jbuck2005/brio_compatible_builder_series/stl_files/beams/beam_slotted_20.stl

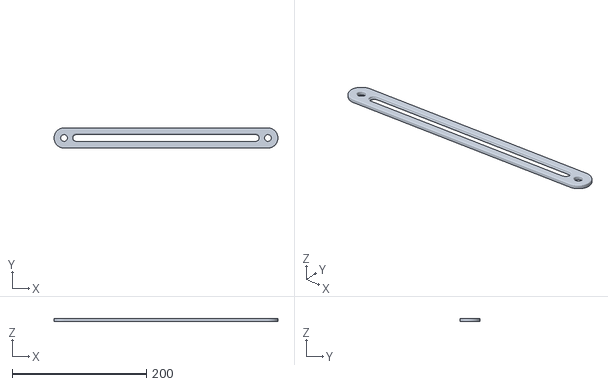
[picture p25: CAD file, 2021-01-02]
stl_files/beams/beam_slotted_20.stl
334.0 x 30.0 x 5.00
