jbuck2005/brio_compatible_builder_series/stl_files/gears/gear_double_idler_20_25.stl

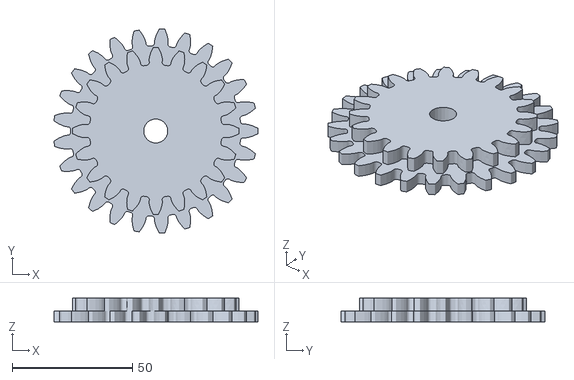
[picture p26: CAD file, 2021-01-02]
stl_files/gears/gear_double_idler_20_25.stl
84.8 x 85.0 x 9.90
