jbuck2005/brio_compatible_builder_series/stl_files/wheels_and_pulleys/pulley_v_60mm.stl

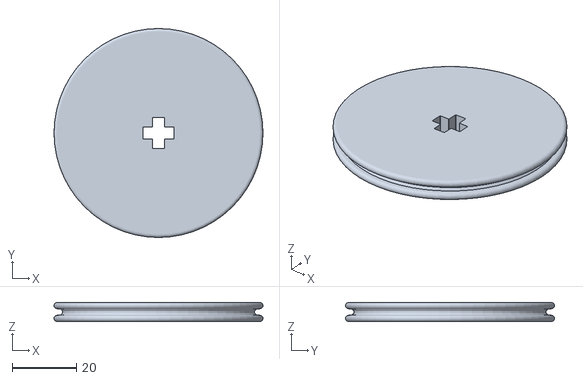
[picture p27: CAD file, 2021-01-03]
stl_files/wheels_and_pulleys/pulley_v_60mm.stl
65.3 x 65.3 x 6.00
