jbuck2005/brio_compatible_builder_series/stl_files/wheels_and_pulleys/pulley_v_40mm.stl

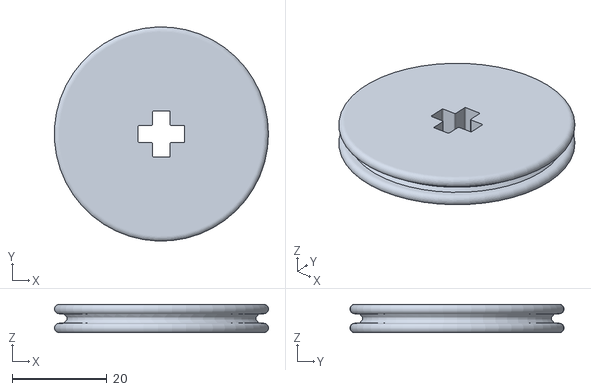
[picture p30: CAD file, 2021-01-03]
stl_files/wheels_and_pulleys/pulley_v_40mm.stl
45.2 x 45.2 x 6.00
