jbuck2005/brio_compatible_builder_series/stl_files/gears/gear_double_cross_10_15.stl

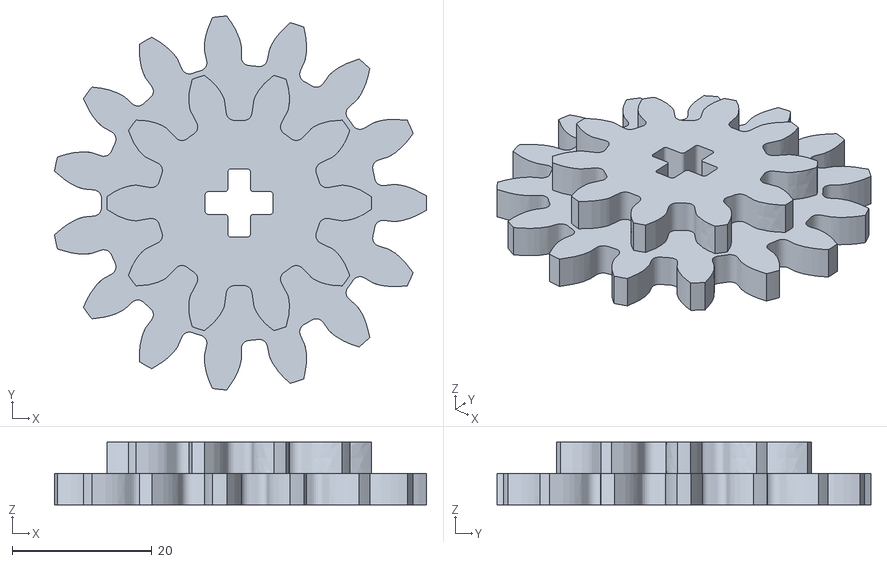
[picture p32: CAD file, 2021-01-02]
stl_files/gears/gear_double_cross_10_15.stl
53.2 x 53.4 x 9.00
