jbuck2005/brio_compatible_builder_series/stl_files/wheels_and_pulleys/pulley_v_70mm.stl

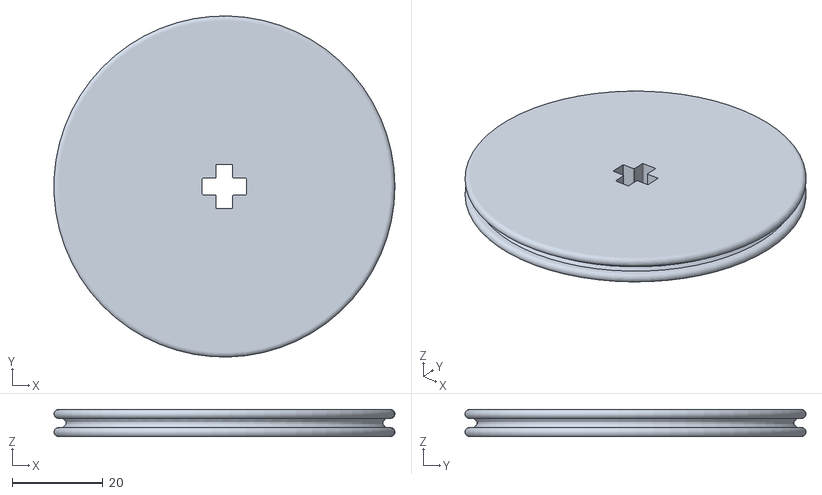
[picture p33: CAD file, 2021-01-03]
stl_files/wheels_and_pulleys/pulley_v_70mm.stl
75.2 x 75.2 x 6.00
