jbuck2005/brio_compatible_builder_series/stl_files/wheels_and_pulleys/pulley_v_50mm.stl

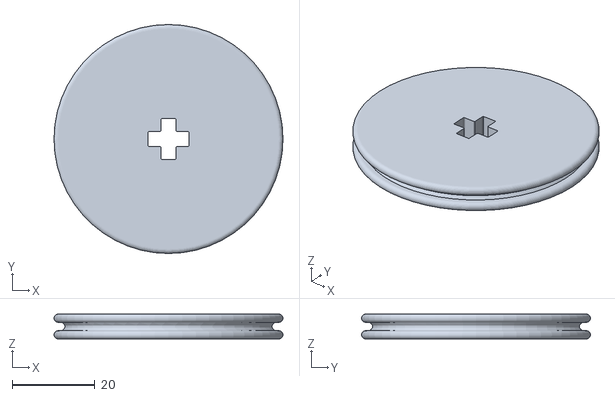
[picture p36: CAD file, 2021-01-03]
stl_files/wheels_and_pulleys/pulley_v_50mm.stl
55.3 x 55.3 x 6.00
