jbuck2005/brio_compatible_builder_series/stl_files/beams/beam_slotted_14.stl

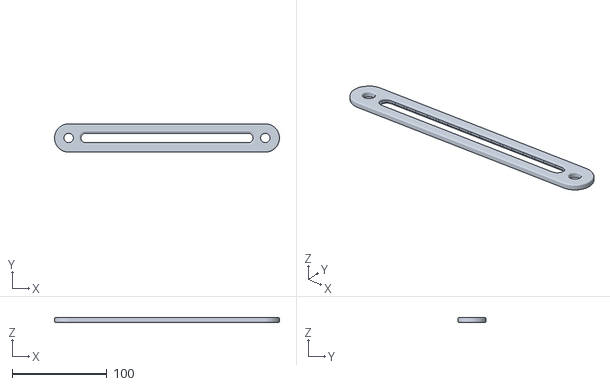
[picture p37: CAD file, 2021-01-02]
stl_files/beams/beam_slotted_14.stl
238.0 x 30.0 x 5.00
