jbuck2005/brio_compatible_builder_series/stl_files/gears/gear_double_idler_10_10.stl

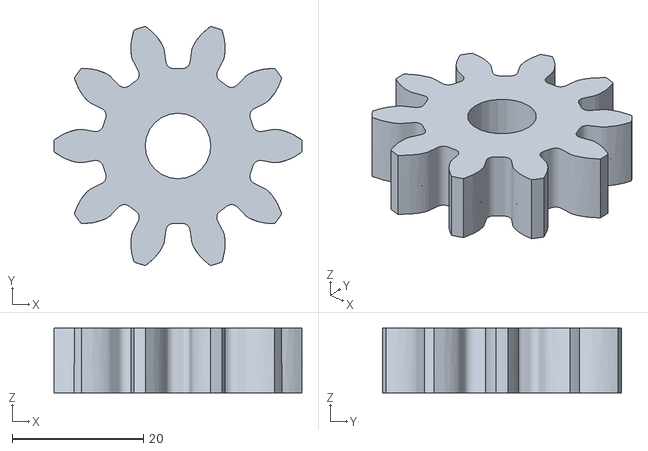
[picture p38: CAD file, 2021-01-02]
stl_files/gears/gear_double_idler_10_10.stl
37.8 x 36.5 x 9.90
