jbuck2005/brio_compatible_builder_series/stl_files/wheels_and_pulleys/pulley_v_46mm.stl

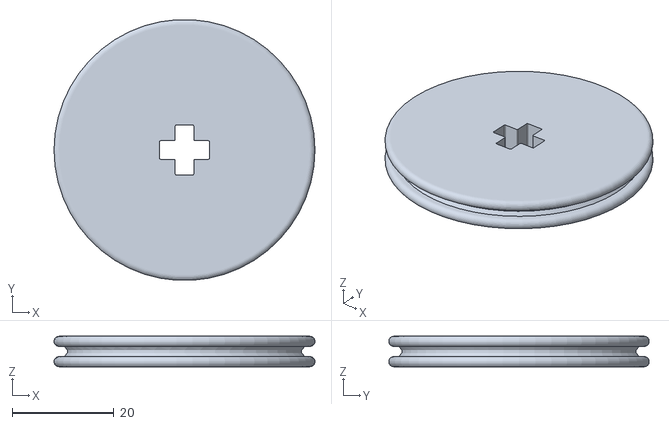
[picture p39: CAD file, 2021-01-03]
stl_files/wheels_and_pulleys/pulley_v_46mm.stl
51.3 x 51.2 x 6.00
