jbuck2005/brio_compatible_builder_series/stl_files/wheels_and_pulleys/pulley_v_100mm.stl

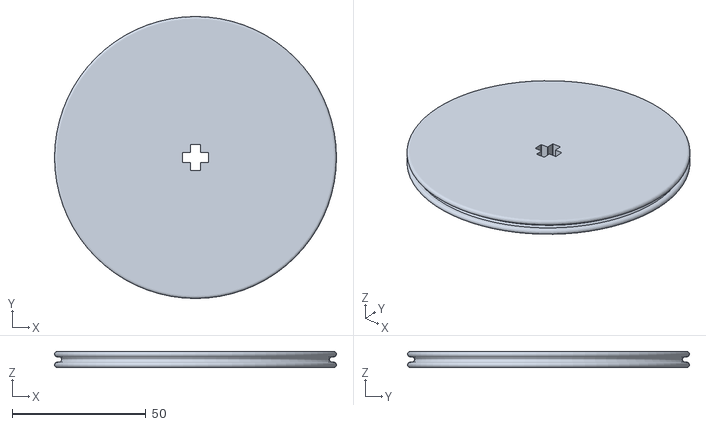
[picture p41: CAD file, 2021-01-03]
stl_files/wheels_and_pulleys/pulley_v_100mm.stl
105.3 x 105.3 x 6.00
