jbuck2005/brio_compatible_builder_series/stl_files/wheels_and_pulleys/pulley_v_20mm.stl

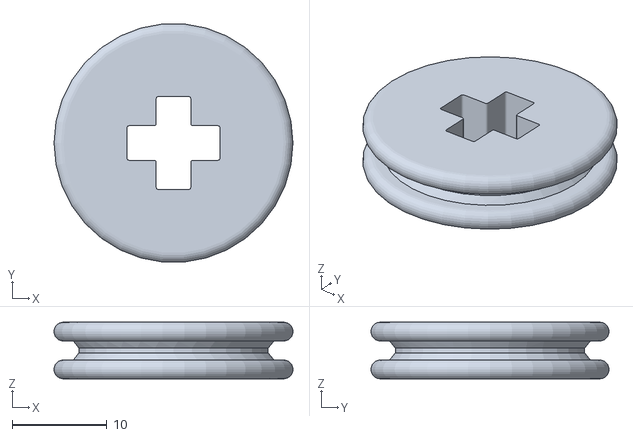
[picture p44: CAD file, 2021-01-03]
stl_files/wheels_and_pulleys/pulley_v_20mm.stl
25.3 x 25.2 x 6.00
