jbuck2005/brio_compatible_builder_series/stl_files/beams/beam_normal_09.stl

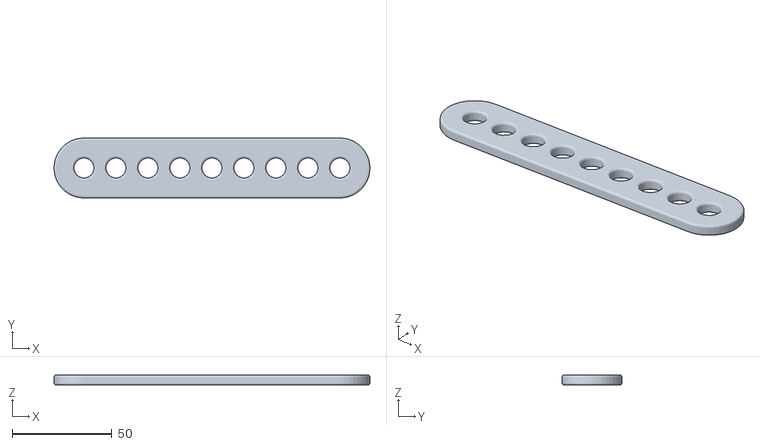
[picture p51: CAD file, 2021-01-02]
stl_files/beams/beam_normal_09.stl
158.0 x 30.0 x 5.00
