jbuck2005/brio_compatible_builder_series/stl_files/gears/gear_double_idler_15_20.stl

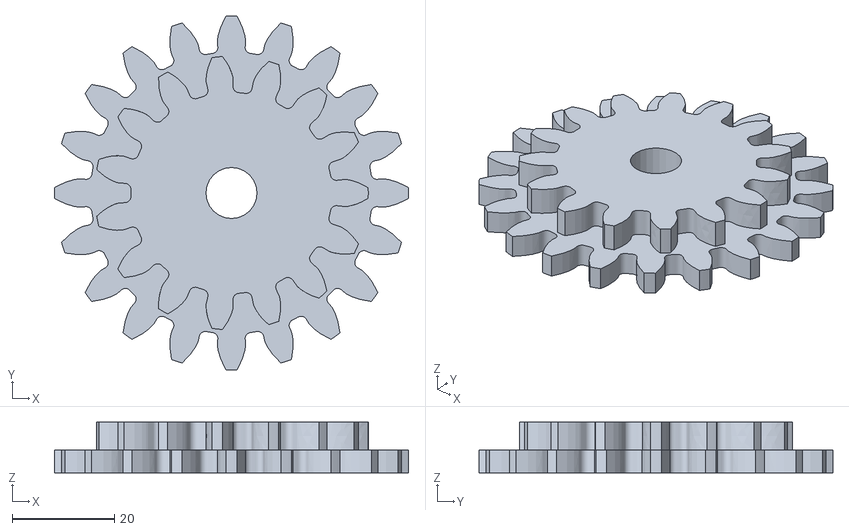
[picture p52: CAD file, 2021-01-02]
stl_files/gears/gear_double_idler_15_20.stl
69.3 x 69.3 x 9.90
