jbuck2005/brio_compatible_builder_series/stl_files/wheels_and_pulleys/drive_wheel_threaded_post_2.stl

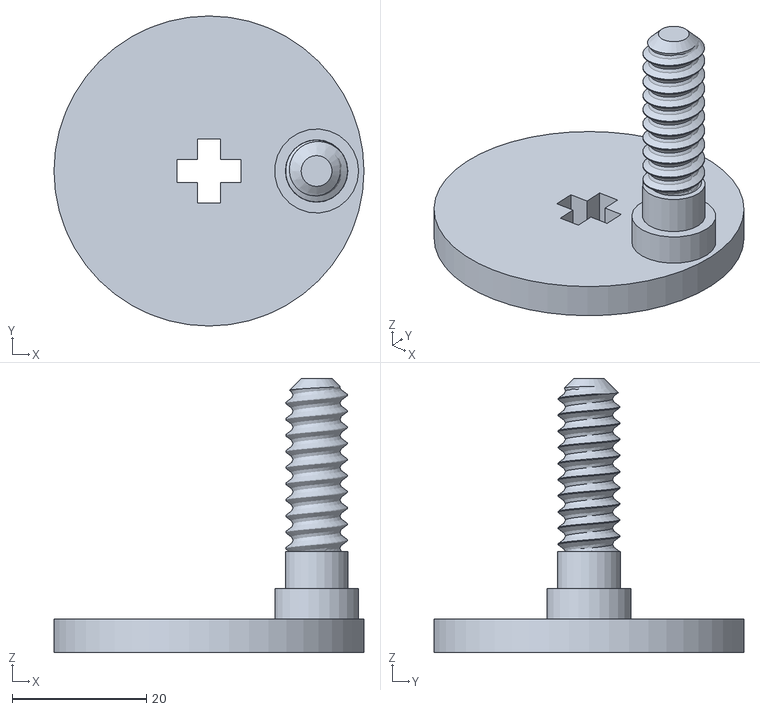
[picture p53: CAD file, 2021-01-02]
stl_files/wheels_and_pulleys/drive_wheel_threaded_post_2.stl
46.1 x 46.1 x 40.8
