jbuck2005/brio_compatible_builder_series/stl_files/wheels_and_pulleys/drive_wheel_double_post.stl

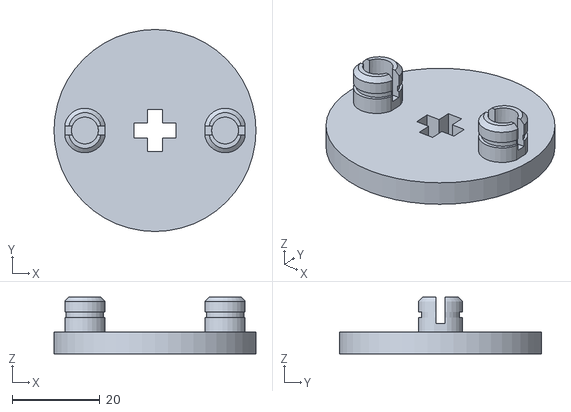
[picture p55: CAD file, 2021-01-02]
stl_files/wheels_and_pulleys/drive_wheel_double_post.stl
46.1 x 46.1 x 13.0
