jbuck2005/brio_compatible_builder_series/stl_files/gears/gear_single_cross_25.stl

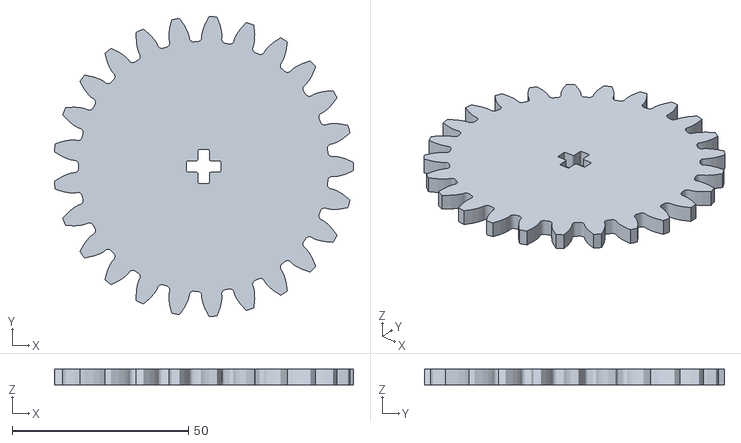
[picture p57: CAD file, 2021-01-02]
stl_files/gears/gear_single_cross_25.stl
84.8 x 85.0 x 4.50
