jbuck2005/brio_compatible_builder_series/stl_files/beams/beam_normal_06.stl

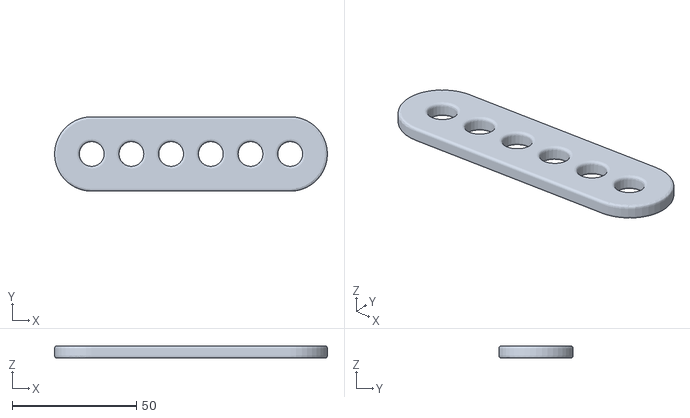
[picture p58: CAD file, 2021-01-02]
stl_files/beams/beam_normal_06.stl
110.0 x 30.0 x 5.00
