jbuck2005/brio_compatible_builder_series/stl_files/beams/beam_slotted_07.stl

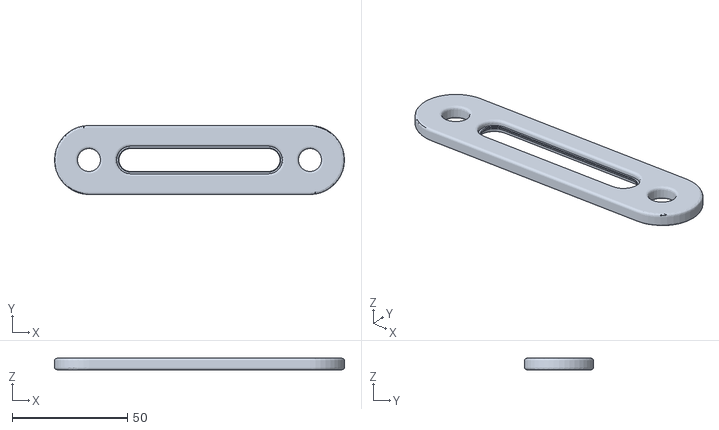
[picture p60: CAD file, 2021-01-02]
stl_files/beams/beam_slotted_07.stl
126.0 x 30.0 x 5.00
