jbuck2005/brio_compatible_builder_series/stl_files/gears/gear_single_cross_15.stl

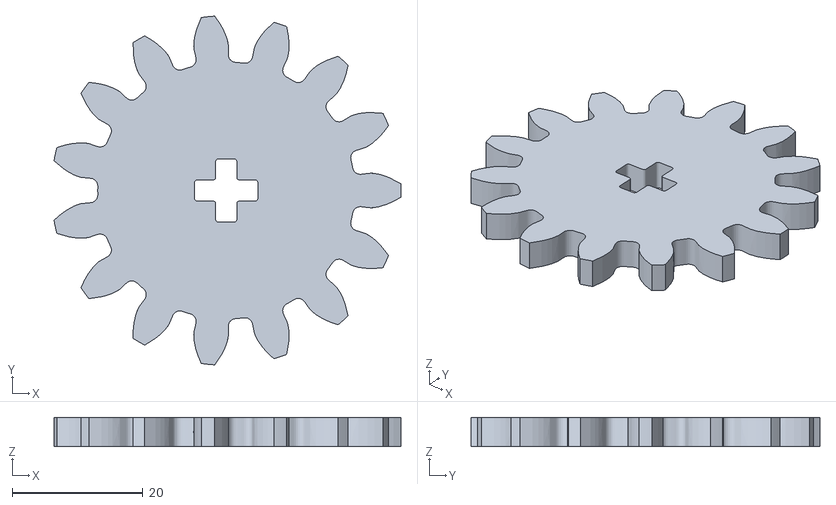
[picture p63: CAD file, 2021-01-02]
stl_files/gears/gear_single_cross_15.stl
53.2 x 53.4 x 4.50
